sylvainlebras/Thermorad/IMG_0604.jpg

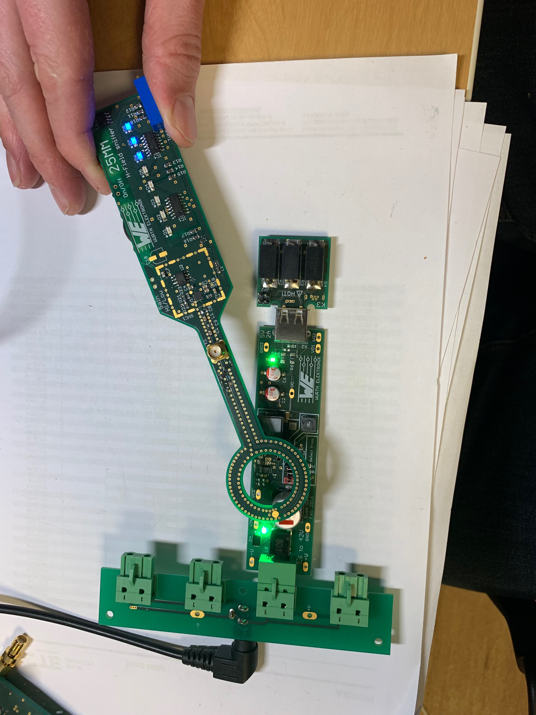
IMG_0604.jpg
